rakesh12shankar/canopy-cold-plate-cht/results/reference/figures/Finer_Transport_Diagnostics.png

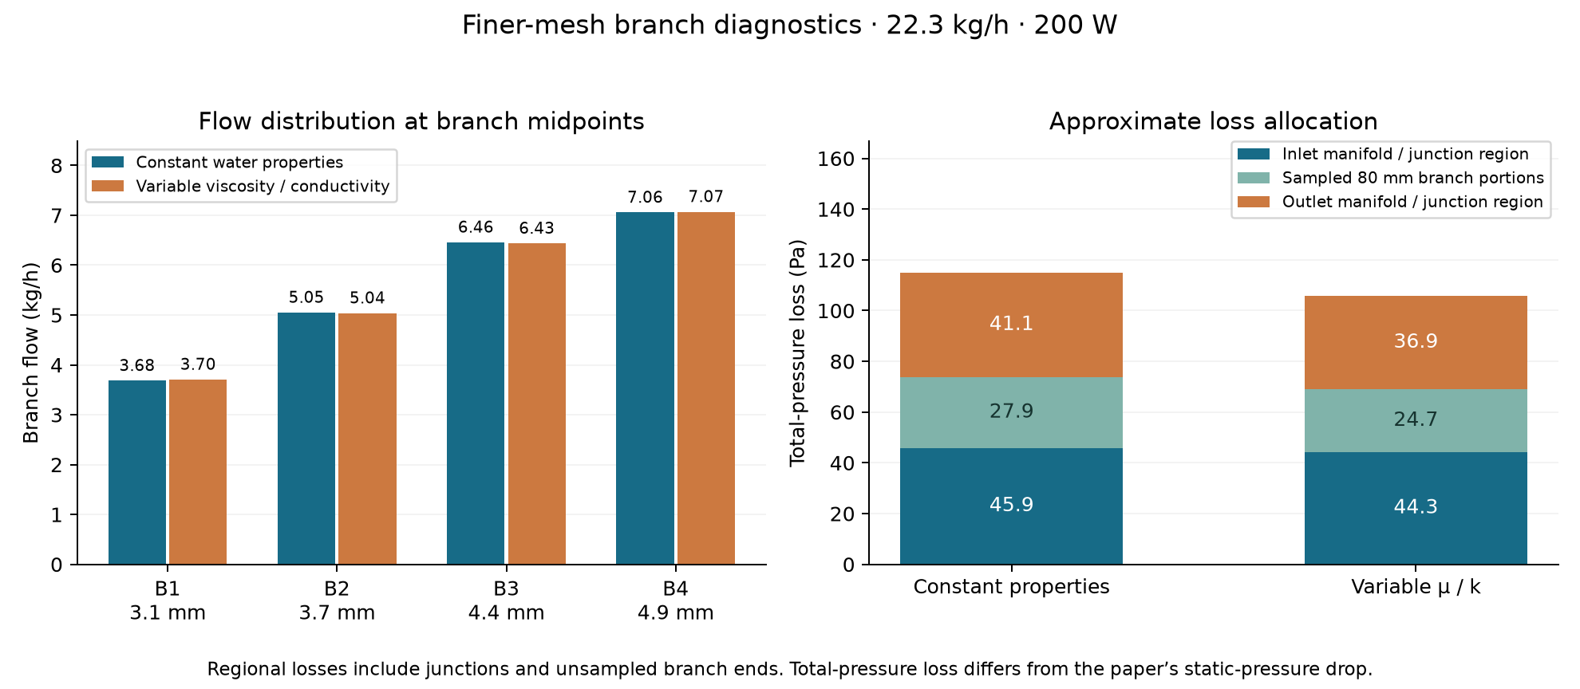
results/reference/figures/Finer_Transport_Diagnostics.png
