rakesh12shankar/canopy-cold-plate-cht/results/reference/figures/Followup_Mesh_Comparison.png

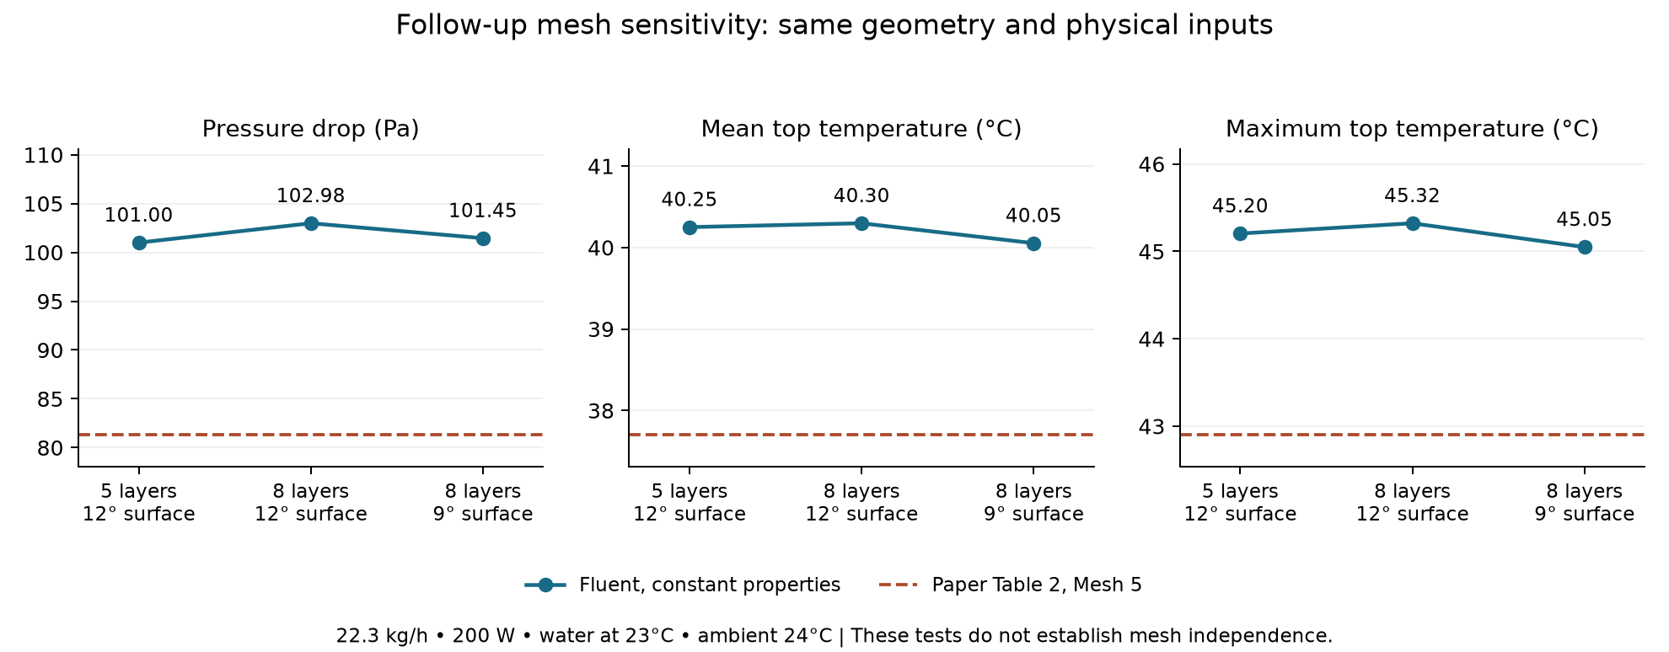
results/reference/figures/Followup_Mesh_Comparison.png
