rakesh12shankar/canopy-cold-plate-cht/results/reference/figures/T2_Coarse_TopTemperature.png

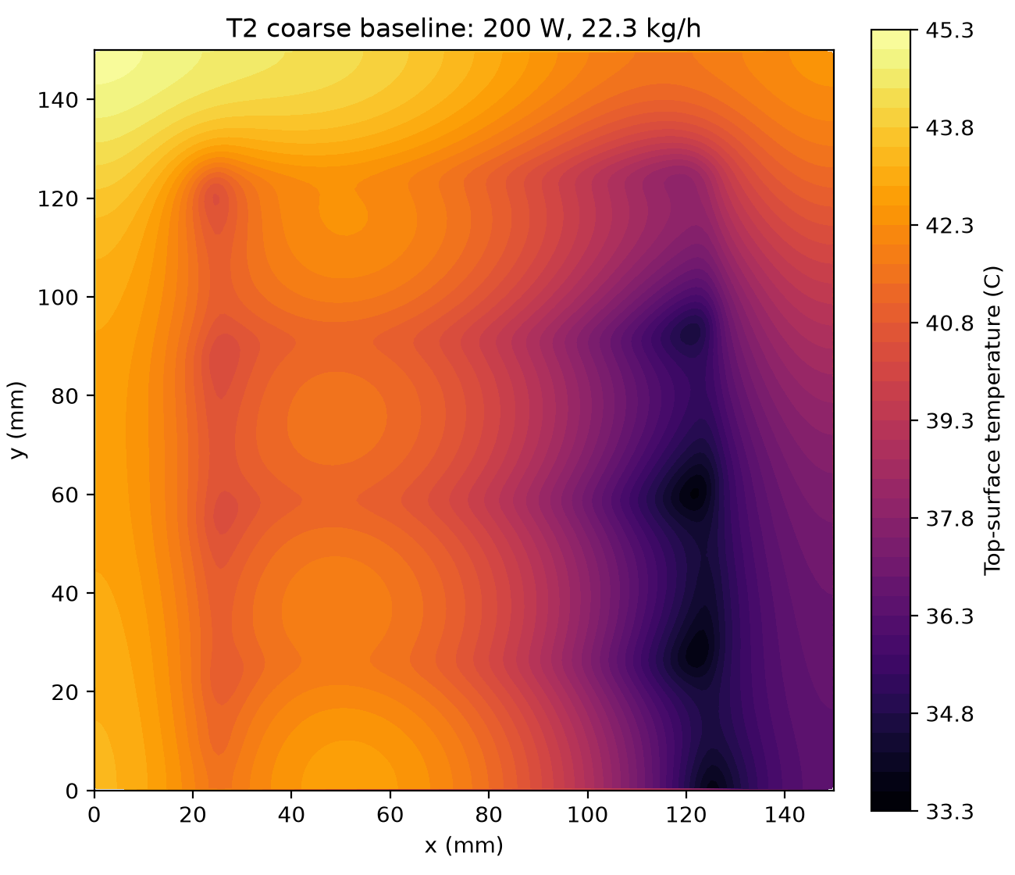
results/reference/figures/T2_Coarse_TopTemperature.png
